stefancristian236/Wien_Bridge_Oscilator/Wien_oscilator.asc

C1: cap; 10p
C6: cap; 940p
C7: cap; 940p
C8: cap; 5µ
C9: cap; 5µ
D1: zener; BZX84C6V2L
D2: diode; 1N4148
D3: diode; 1N4148
D4: diode; 1N4148
D5: diode; 1N4148
D6: diode; 1N4148
D7: diode; 1N4148
D8: diode; 1N4148
D9: diode; 1N4148
D10: diode; 1N4148
D11: diode; 1N4148
J1: njf; J309
Q1: npn; BC817-25
Q2: npn; BC817-25
Q3: npn; BC817-25
Q4: npn; BC817-25
Q5: npn; BC817-25
Q6: npn; BC817-25
Q7: npn; BC817-25
Q8: pnp; BC807-25
Q9: pnp; BC807-25
Q10: pnp; BC807-25
Q11: pnp; BC807-25
Q12: npn; BC817-25
Q13: npn; BC817-25
Q14: pnp; BC807-25
Q15: npn; BC817-25
Q16: npn; BC817-25
Q17: npn; BC817-25
Q18: npn; BC817-25
Q19: pnp; BC807-25
Q20: npn; BC817-25
Q21: pnp; BC807-25
R1: res; 4.7k
R2: res; 330
R3: res; 330
R4: res; 300m
R5: res; 300m
R6: res; 330
R7: res; 180
R8: res; 180
R9: res; 1.2k
R10: res; 600
R11: res; 75
R12: res; 180
R21: res; 20k
R22: res; 20k
R23: res; 10k
R24: res; 800
R25: res; 10k
R26: res; 32.5k
V2: voltage; 12
Named nets: v_in, 0
.tran 0 10m 0 0.0001
.op
